ckfnr/Projekt-Debbie/Images/back_view.png

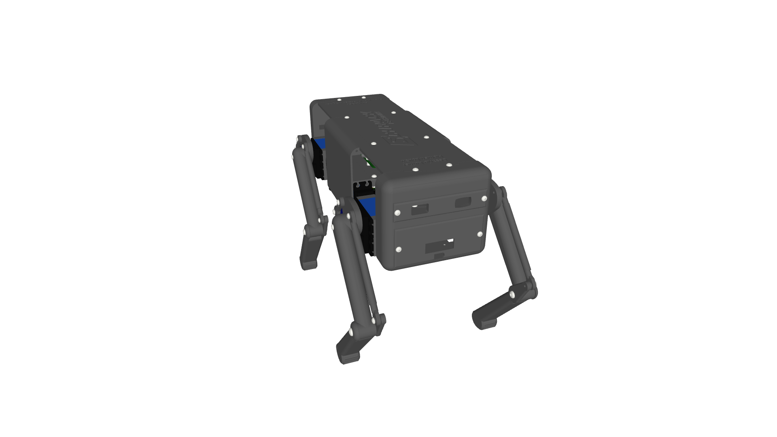
Images/back_view.png
