ckfnr/Projekt-Debbie/Images/Coord_calculation.png

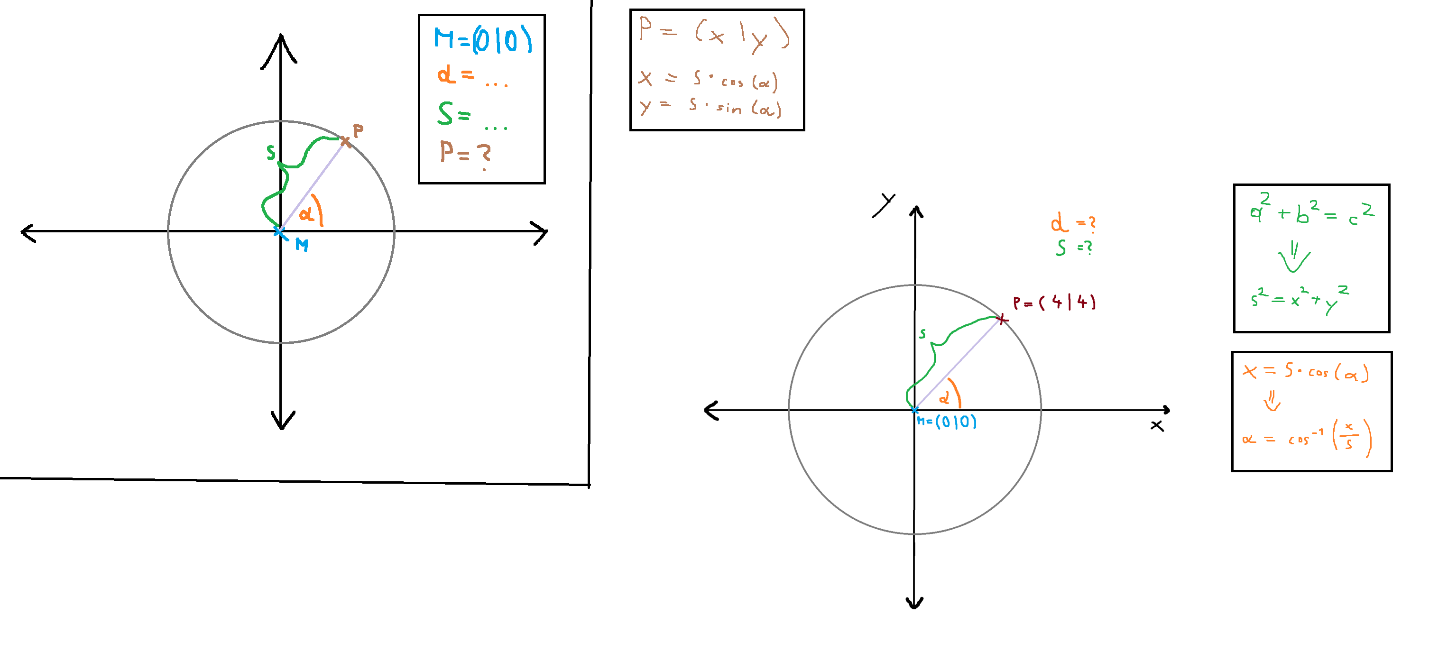
Images/Coord_calculation.png
