ckfnr/Projekt-Debbie/Images/Direction.png

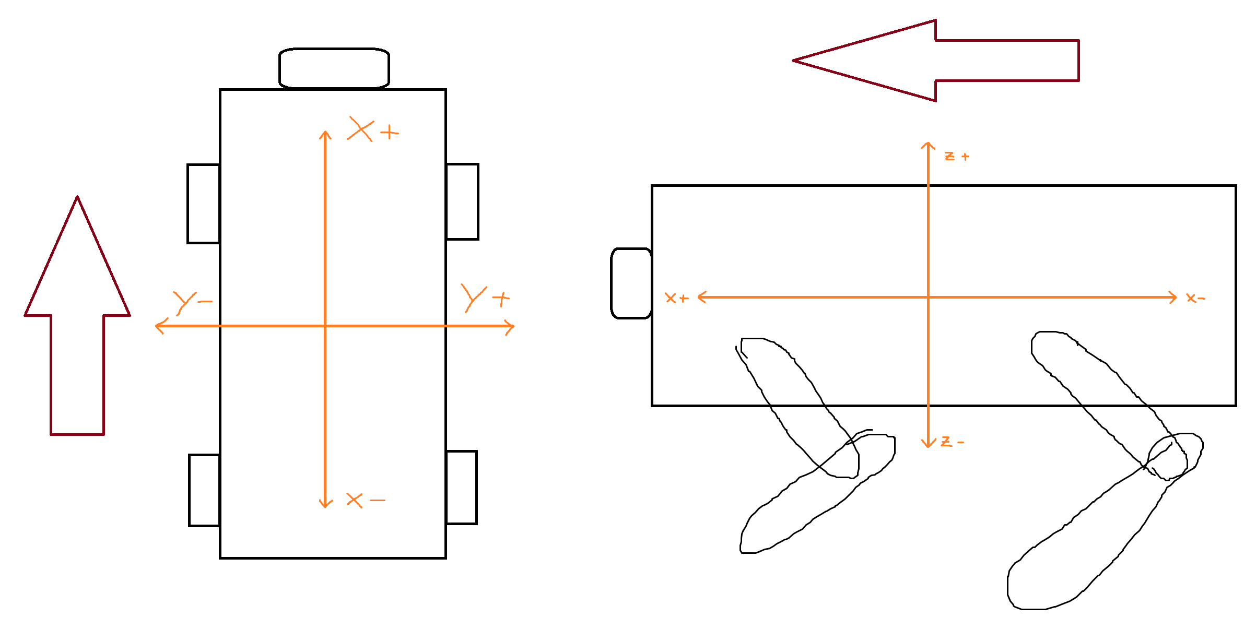
Images/Direction.png
