ckfnr/Projekt-Debbie/Images/Feet.png

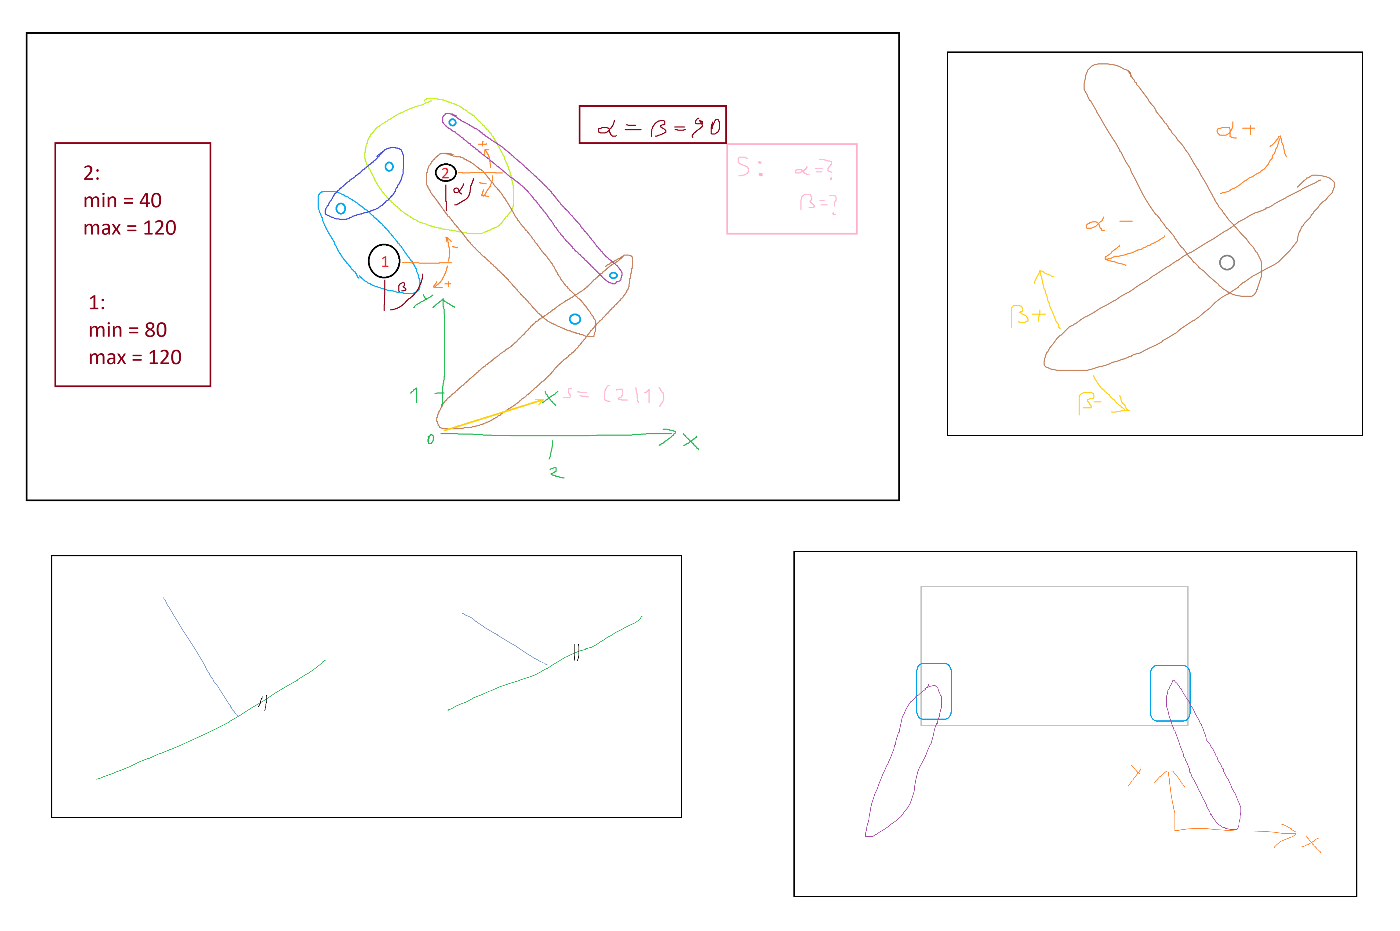
Images/Feet.png
