ckfnr/Projekt-Debbie/Images/Leg_new.png

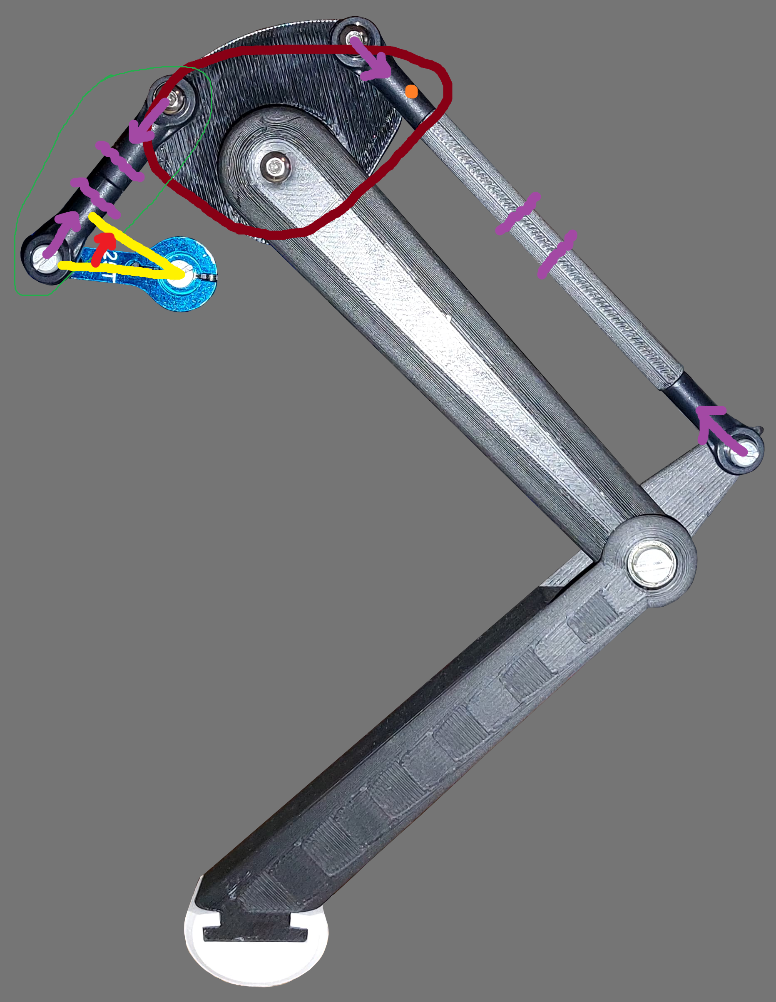
Images/Leg_new.png
