ckfnr/Projekt-Debbie/Images/Movement_illustration.png

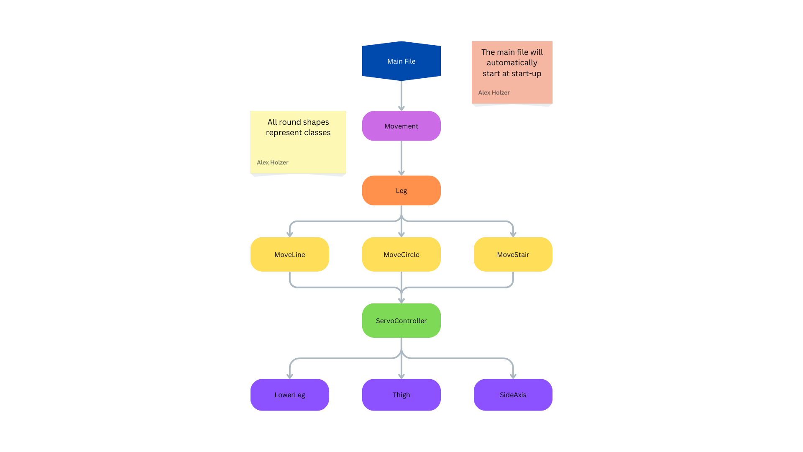
Images/Movement_illustration.png
