ckfnr/Projekt-Debbie/Images/Screenshot 2025-02-16 170329.png

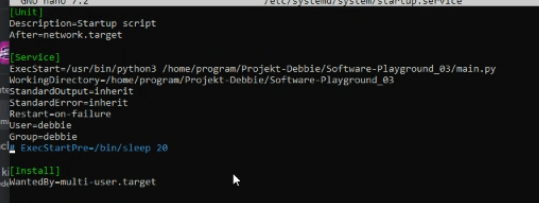
Images/Screenshot 2025-02-16 170329.png
