ckfnr/Projekt-Debbie/Images/side_view_1.png

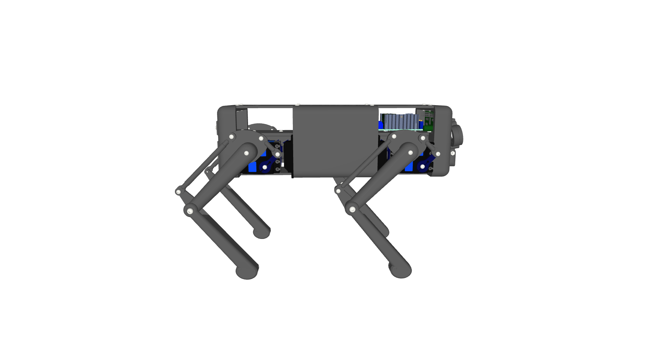
Images/side_view_1.png
