ckfnr/Projekt-Debbie/Images/xyz_calculations_point-n.jpg

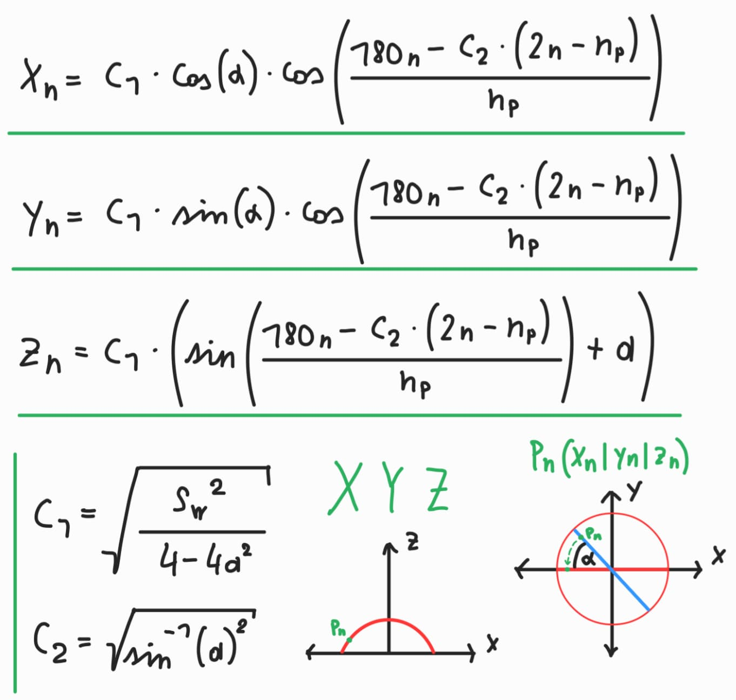
Images/xyz_calculations_point-n.jpg
