ckfnr/Projekt-Debbie/Images/z=0_Movement.png

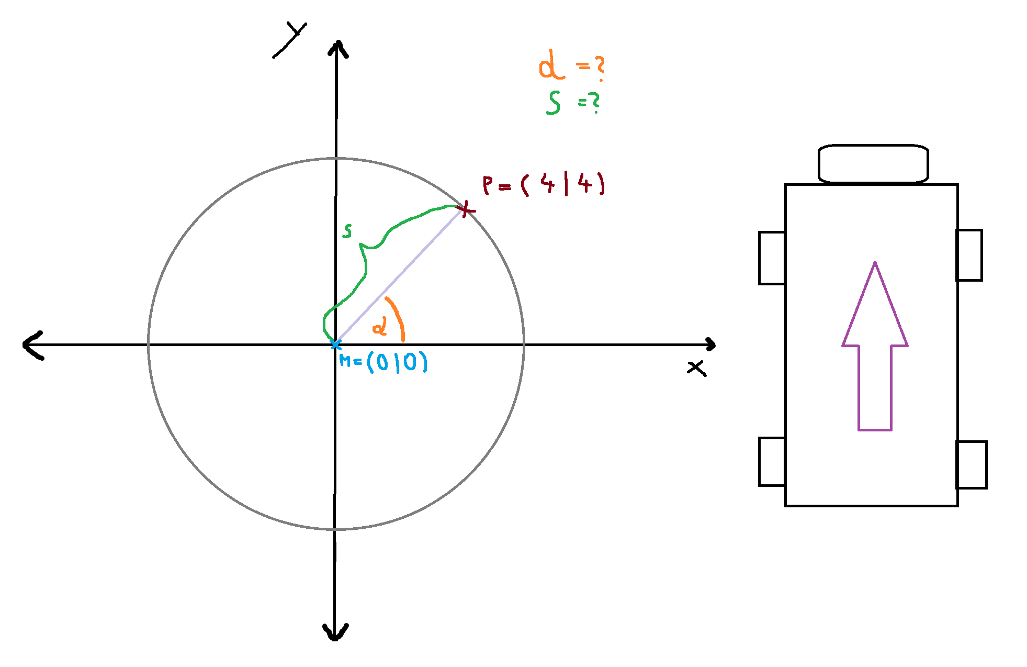
Images/z=0_Movement.png
