ckfnr/Projekt-Debbie/Hardware/Battery/protection_circuit_wiring.png

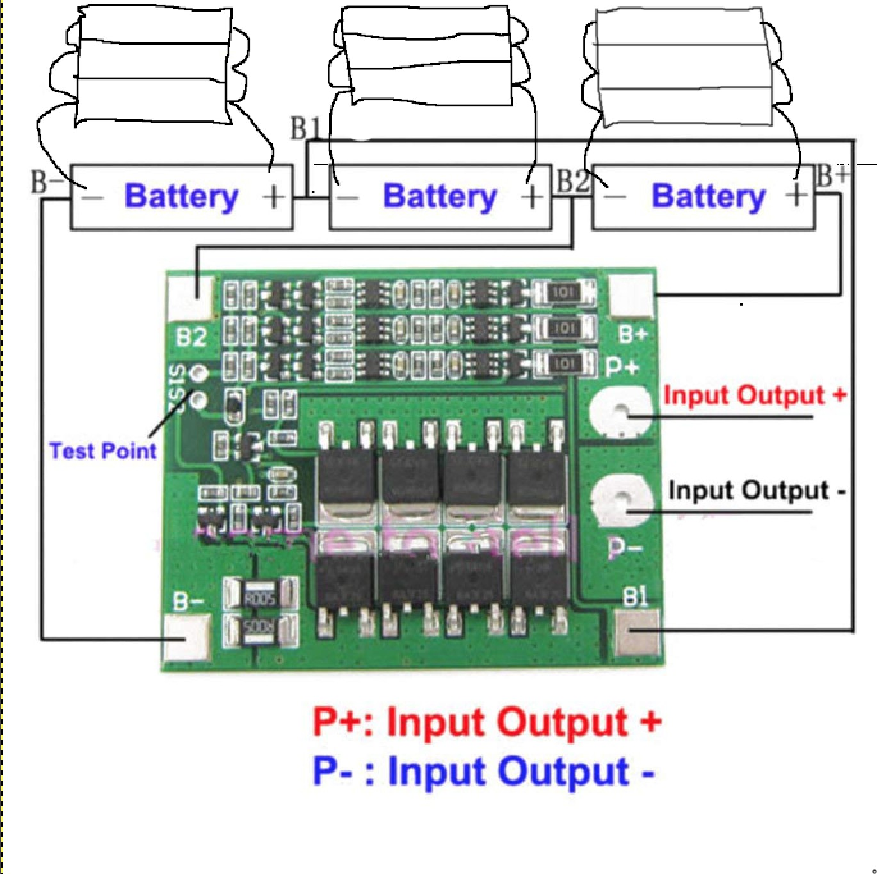
Hardware/Battery/protection_circuit_wiring.png
