ckfnr/Projekt-Debbie/Images/MaxStepWidth.png

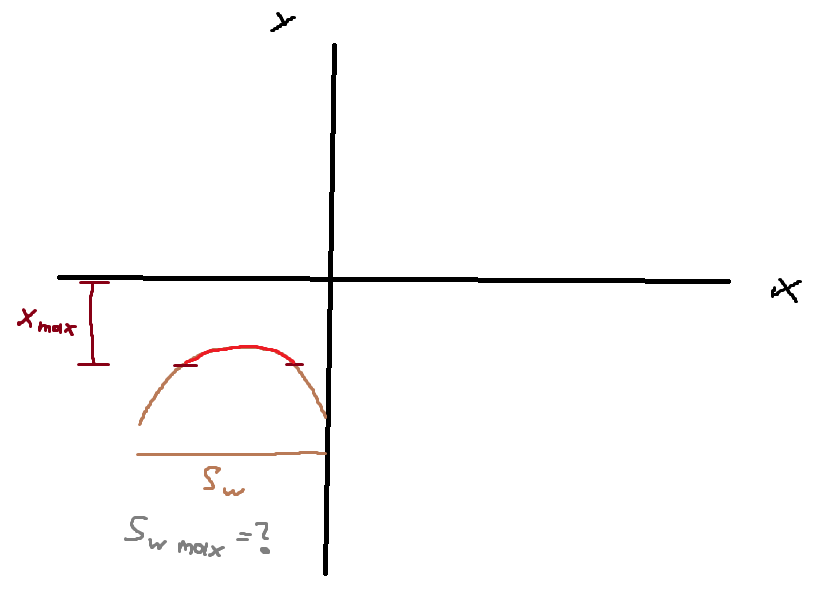
Images/MaxStepWidth.png
