ckfnr/Projekt-Debbie/Images/Thigh_construction.png

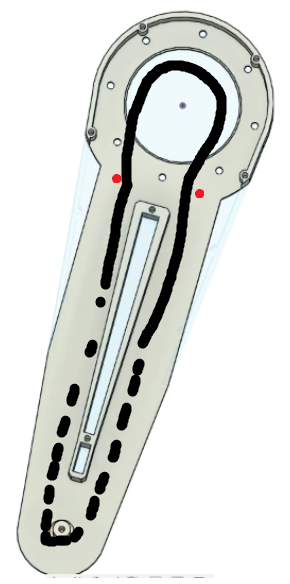
Images/Thigh_construction.png
