ckfnr/Projekt-Debbie/Images/Upper_step_movement.png

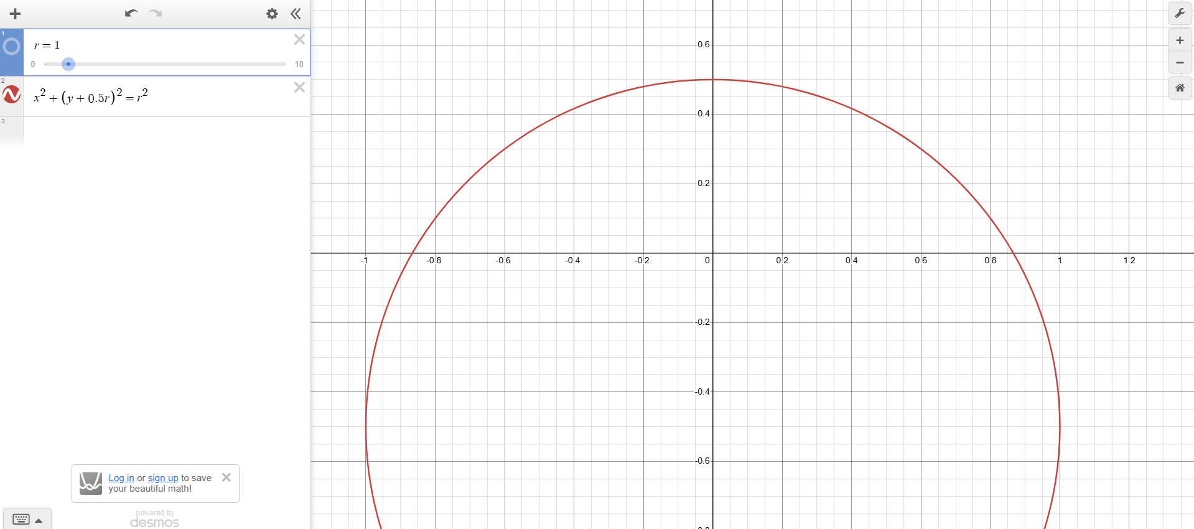
Images/Upper_step_movement.png
